Raziz1/Audio_Amplifier/LTSpice_simulations/Audio_Amplifier_DC_Bias.asc

C1: cap; 100µ
C2: cap; 4700µ
C3: cap; 10µ
C4: cap; 10µ
D1: diode; 1N4148
D2: diode; 1N4148
M1: pmos; IRF9640
M2: nmos; IRF2805S
R1: res; 8k
R2: res; 1k
R3: res; 100k
R4: res; 100k
R5: res; 4
R6: res; 1Meg
R7: res; 10k
R8: res; 10k
U1: LT1124
U2: LT1124
V1: voltage; SINE(0 1 1k 0); AC 1
V3: voltage; 30
Named nets: 0
.tran 0.01
.ac dec 1000 1 20k
DC Blocking Cap
High Pass Filter
Fc: 1.58Hz
x8 Gain Stage
High Pass Filter:
Fc: 8.46Hz
Speaker
Push Pull Power Stage
Unity Gain Buffer
with negative feedback
Injection Resistor
DC Biasing Circuit
