Raziz1/Audio_Amplifier/LTSpice_simulations/Class A/Class_A_Audio_Amplifier.asc

C2: cap; 10µ
Q1: npn; 2SCR563F3
Q2: npn; 2SCR563F3
R1: res; 100k
R2: res; 10k
R3: res; 1k
R4: res; 100
R5: res; 100k
R6: res; 10k
R7: res; 4
R8: res; 1.5k
U2: LT1677
V1: voltage; 30
V3: voltage; SINE(0 1 100); AC 1
Named nets: 0
.tran 0 1.025 1
.ac dec 1000 1 20k
Audio Input
DC Blocking Cap
Transistor Bias
x10 Gain
Unity Gain Buffer
Power Amplifier Stage
Speaker
Transistor Bias
