Raziz1/Audio_Amplifier/LTSpice_simulations/Class AB/Dual Supply/Class_AB_Audio_Amplifier_Dual_Supply.asc

C1: cap; 1n
C2: cap; 10µ
D1: diode; 1N4148
D2: diode; 1N4148
R1: res; 9k
R2: res; 1k
R4: res; 4
R5: res; 10k
R6: res; 10k
R7: res; 1k
U1: LT1124
U2: LT1124
U3: irfz34n
U4: irf9z24n
V1: voltage; SINE(0 1 100 0); AC 1
V2: voltage; -20V
V3: voltage; 20V
Named nets: 0
.tran 0.1
.ac dec 1000 1 20k
+20V Supply Rail
-20V Supply Rail
Speaker
Power Amplifier Stage
Transistor Biasing
Unity Gain Buffer
with Negative Feedback
x9 Gain
Low Pass Filter
Fc: 159kHz
